guiplayer/monza-aldl-dashboard/sketch/monza-aldl-dashboard/icones.h

#ifndef ICONES_H
#define ICONES_H

#include <Arduino.h>

// Ícone: Velocímetro (16x16)
const unsigned char icone_dash[] PROGMEM = {
	0x00, 0x00, 0x00, 0x00, 0x00, 0x00, 0x00, 0x7e, 0x00, 0x01, 0xff, 0x80, 0x03, 0x00, 0xc0, 0x06, 
	0x00, 0x60, 0x0c, 0x00, 0x30, 0x18, 0x00, 0x18, 0x10, 0x00, 0x08, 0x30, 0x03, 0x0c, 0x30, 0x03, 
	0x0c, 0x30, 0x1e, 0x0c, 0x30, 0x3c, 0x0c, 0x30, 0x18, 0x0c, 0x30, 0x18, 0x0c, 0x10, 0x00, 0x08, 
	0x18, 0x00, 0x18, 0x0c, 0x7e, 0x30, 0x06, 0x7e, 0x60, 0x00, 0x00, 0x00, 0x00, 0x00, 0x00, 0x00, 
	0x00, 0x00, 0x00, 0x00, 0x00, 0x00, 0x00, 0x00
};

// Ícone: Motor/Check Engine (16x16)
const unsigned char icone_engine[] PROGMEM = {
	0x00, 0x00, 0x00, 0x00, 0x00, 0x00, 0x07, 0xfc, 0x00, 0x0c, 0x06, 0x00, 0x0c, 0x00, 0x00, 0x68, 
	0x07, 0xe0, 0x78, 0x0c, 0x70, 0x3f, 0xd8, 0x10, 0x26, 0x10, 0x98, 0x3f, 0xd2, 0xe8, 0x7f, 0xf3, 
	0x88, 0x7f, 0xd6, 0x88, 0x7f, 0xd8, 0x18, 0x30, 0x0c, 0x30, 0x30, 0x07, 0xf0, 0x00, 0x00, 0x30, 
	0x00, 0x00, 0x3c, 0x00, 0x00, 0x3c, 0x00, 0x00, 0x1e, 0x00, 0x00, 0x1e, 0x00, 0x00, 0x0e, 0x00, 
	0x00, 0x0e, 0x00, 0x00, 0x00, 0x00, 0x00, 0x00
};

// Ícone: Engrenagem (16x16)
const unsigned char icone_config[] PROGMEM = {
	0x00, 0x3c, 0x00, 0x00, 0x34, 0x00, 0x00, 0x24, 0x00, 0x0e, 0x66, 0x70, 0x1b, 0xc3, 0xd8, 0x10, 
	0x00, 0x0c, 0x18, 0x7e, 0x18, 0x08, 0xc3, 0x10, 0x09, 0x88, 0x90, 0x1b, 0x3c, 0xd8, 0xf2, 0x66, 
	0x4f, 0xc2, 0x43, 0x43, 0x82, 0xc3, 0x41, 0xf2, 0x66, 0x4f, 0x1b, 0x3c, 0xd8, 0x09, 0x18, 0x90, 
	0x08, 0xc3, 0x10, 0x18, 0x7e, 0x18, 0x10, 0x00, 0x08, 0x1b, 0xc3, 0xd8, 0x0e, 0x66, 0x70, 0x04, 
	0x24, 0x00, 0x00, 0x34, 0x00, 0x00, 0x3c, 0x00
};

// Ícone: Sensor/Chip (16x16)
const unsigned char icone_sensor[] PROGMEM = {
	0x00, 0x00, 0x00, 0x00, 0x00, 0x00, 0x00, 0x00, 0x00, 0x00, 0x00, 0x00, 0x01, 0x52, 0x80, 0x03, 
	0xff, 0xc0, 0x07, 0xff, 0xe0, 0x0e, 0x2d, 0xf0, 0x0e, 0x00, 0x60, 0x0e, 0x80, 0x70, 0x0e, 0x00, 
	0x60, 0x0e, 0x20, 0x70, 0x0e, 0x02, 0x70, 0x0e, 0x00, 0x60, 0x0e, 0x00, 0x70, 0x0e, 0x08, 0x60, 
	0x0e, 0x00, 0x70, 0x07, 0xff, 0xe0, 0x07, 0xff, 0xc0, 0x01, 0x7f, 0x80, 0x00, 0x00, 0x00, 0x00, 
	0x00, 0x00, 0x00, 0x00, 0x00, 0x00, 0x00, 0x00
};

// Ícone de Sucesso (Check) 16x16
const unsigned char icone_ok[] PROGMEM = {
  0x00, 0x00, 0x00, 0x00, 0x00, 0x01, 0x00, 0x03, 0x00, 0x07, 0x00, 0x0e, 0x00, 0x1c, 0x00, 0x38,
  0x00, 0x70, 0x40, 0xe0, 0x61, 0xc0, 0x73, 0x80, 0x3f, 0x00, 0x1e, 0x00, 0x0c, 0x00, 0x00, 0x00
};

// Ícone de Erro (X) 16x16
const unsigned char icone_erro[] PROGMEM = {
  0x00, 0x00, 0x40, 0x02, 0x60, 0x06, 0x30, 0x0c, 0x18, 0x18, 0x0c, 0x30, 0x06, 0x60, 0x03, 0xc0,
  0x03, 0xc0, 0x06, 0x60, 0x0c, 0x30, 0x18, 0x18, 0x30, 0x0c, 0x60, 0x06, 0x40, 0x02, 0x00, 0x00
};

// Ícone: Mascote / Monzagotchi (24x24)
const unsigned char icone_mascote [] PROGMEM = {
	0x00, 0x00, 0x00, 0x00, 0x00, 0x00, 0x00, 0x00, 0x00, 0x0c, 0x00, 0x30, 0x0e, 0x00, 0x70, 0x0b, 
	0x00, 0xd0, 0x09, 0x81, 0x90, 0x08, 0xff, 0x10, 0x0b, 0x81, 0xd0, 0x0e, 0x00, 0x70, 0x0c, 0x00, 
	0x30, 0x0c, 0xc3, 0x30, 0x0c, 0xc3, 0x30, 0x08, 0x42, 0x10, 0x08, 0x00, 0x10, 0x0c, 0x18, 0x30, 
	0x04, 0x5a, 0x20, 0x06, 0x24, 0x60, 0x03, 0x00, 0xc0, 0x01, 0xc3, 0x80, 0x00, 0x7e, 0x00, 0x00, 
	0x00, 0x00, 0x00, 0x00, 0x00, 0x00, 0x00, 0x00
};

#endif
